liliumjsn/Edifier_R1280T_IR_Hack/Photos/IMG_20220609_170533.jpg

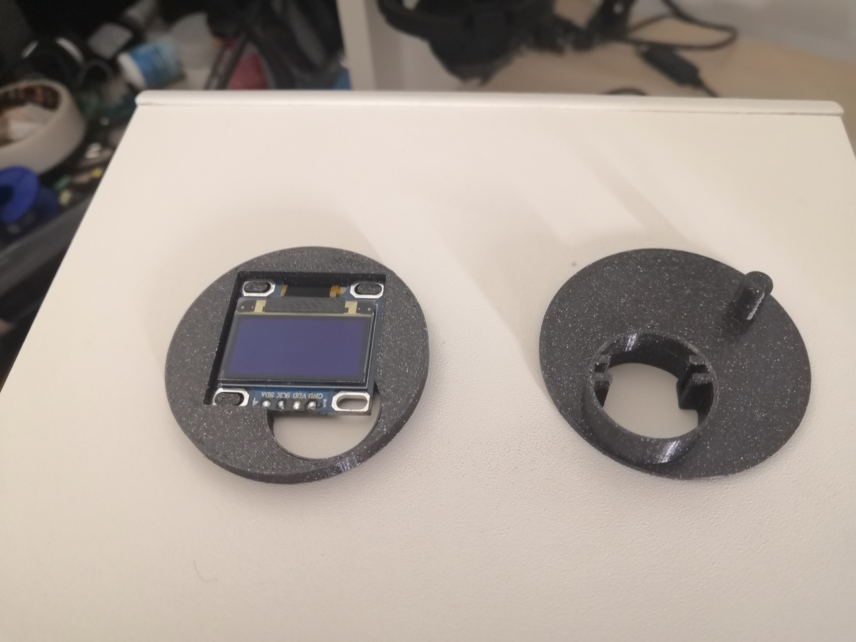
Photos/IMG_20220609_170533.jpg
