liliumjsn/Edifier_R1280T_IR_Hack/Software/src/icons.h

#include <Arduino.h>

// 'wifi_off_icon', 15x15px
const unsigned char epd_bitmap_wifi_off_icon [] PROGMEM = {
  0x01, 0x00, 0xF3, 0x07, 0x0E, 0x18, 0x0E, 0x20, 0x19, 0x40, 0xF0, 0x07, 
  0x6C, 0x18, 0xC2, 0x20, 0x80, 0x01, 0xE0, 0x03, 0x18, 0x0E, 0x00, 0x0C, 
  0xC0, 0x19, 0xC0, 0x31, 0xC0, 0x61, };
// 'wifi_on_icon', 15x15px
const unsigned char epd_bitmap_wifi_on_icon [] PROGMEM = {
  0x00, 0x00, 0xF0, 0x07, 0x0C, 0x18, 0x02, 0x20, 0x01, 0x40, 0xF0, 0x07, 
  0x0C, 0x18, 0x02, 0x20, 0x00, 0x00, 0xE0, 0x03, 0x18, 0x0C, 0x00, 0x00, 
  0xC0, 0x01, 0xC0, 0x01, 0xC0, 0x01, };

// 'mqtt_ok_icon', 15x15px
const unsigned char epd_bitmap_mqtt_ok_icon [] PROGMEM = {
  0x00, 0x00, 0x00, 0x00, 0x00, 0x00, 0x0C, 0x30, 0x1C, 0x38, 0x3C, 0x3C, 
  0x6C, 0x36, 0xCC, 0x33, 0x8C, 0x31, 0x0C, 0x30, 0x0C, 0x30, 0x0C, 0x30, 
  0x0C, 0x30, 0x00, 0x00, 0x00, 0x00, };

// 'mqtt_failed_icon', 15x15px
const unsigned char epd_bitmap_mqtt_failed_icon [] PROGMEM = {
  0x00, 0x00, 0x00, 0x00, 0xF8, 0x1F, 0xF8, 0x1F, 0x18, 0x00, 0x18, 0x00, 
  0x18, 0x00, 0xF8, 0x07, 0xF8, 0x07, 0x18, 0x00, 0x18, 0x00, 0x18, 0x00, 
  0x18, 0x00, 0x18, 0x00, 0x00, 0x00, };

// 'mute_icon', 50x50px
const uint8_t epd_bitmap_mute_icon [] PROGMEM = {
	0x00, 0x00, 0x00, 0x00, 0x00, 0x00, 0x00, 0x00, 0x00, 0x00, 0x00, 0x00, 
  0x00, 0x00, 0x00, 0x00, 0x00, 0x00, 0x00, 0x00, 0x00, 0x00, 0x00, 0x00, 
  0x00, 0x00, 0x00, 0x00, 0x00, 0x00, 0x00, 0x00, 0x00, 0x00, 0x00, 0x00, 
  0x00, 0x00, 0x18, 0x00, 0x00, 0x00, 0x00, 0x00, 0x00, 0x1C, 0x00, 0x00, 
  0x00, 0x00, 0x00, 0x00, 0x1E, 0x00, 0x00, 0x00, 0x00, 0x00, 0x00, 0x1F, 
  0x00, 0x00, 0x00, 0x00, 0x00, 0x80, 0x1F, 0x00, 0x00, 0x00, 0x00, 0x00, 
  0xC0, 0x1F, 0x00, 0x00, 0x00, 0x00, 0x00, 0xE0, 0x1F, 0x00, 0x00, 0x00, 
  0x00, 0x00, 0xF0, 0x1F, 0x00, 0x00, 0x00, 0x00, 0x00, 0xF8, 0x1F, 0x00, 
  0x00, 0x00, 0x00, 0x00, 0xFC, 0x1F, 0x00, 0x00, 0x00, 0xFE, 0xFF, 0xFF, 
  0x1F, 0x00, 0x00, 0x00, 0xFE, 0xFF, 0xFF, 0x9F, 0x01, 0xC0, 0x00, 0xFE, 
  0xFF, 0xFF, 0x1F, 0x03, 0x60, 0x00, 0xFE, 0xFF, 0xFF, 0x1F, 0x06, 0x30, 
  0x00, 0xFE, 0xFF, 0xFF, 0x1F, 0x0C, 0x18, 0x00, 0xFE, 0xFF, 0xFF, 0x1F, 
  0x18, 0x0C, 0x00, 0xFE, 0xFF, 0xFF, 0x1F, 0x30, 0x06, 0x00, 0xFE, 0xFF, 
  0xFF, 0x1F, 0x60, 0x03, 0x00, 0xFE, 0xFF, 0xFF, 0x1F, 0xC0, 0x01, 0x00, 
  0xFE, 0xFF, 0xFF, 0x1F, 0xC0, 0x01, 0x00, 0xFE, 0xFF, 0xFF, 0x1F, 0x60, 
  0x03, 0x00, 0xFE, 0xFF, 0xFF, 0x1F, 0x30, 0x06, 0x00, 0xFE, 0xFF, 0xFF, 
  0x1F, 0x18, 0x0C, 0x00, 0xFE, 0xFF, 0xFF, 0x1F, 0x0C, 0x18, 0x00, 0xFE, 
  0xFF, 0xFF, 0x1F, 0x06, 0x30, 0x00, 0xFE, 0xFF, 0xFF, 0x1F, 0x03, 0x60, 
  0x00, 0xFE, 0xFF, 0xFF, 0x9F, 0x01, 0xC0, 0x00, 0xFE, 0xFF, 0xFF, 0x1F, 
  0x00, 0x00, 0x00, 0xFE, 0xFF, 0xFF, 0x1F, 0x00, 0x00, 0x00, 0x00, 0x00, 
  0xFC, 0x1F, 0x00, 0x00, 0x00, 0x00, 0x00, 0xF8, 0x1F, 0x00, 0x00, 0x00, 
  0x00, 0x00, 0xF0, 0x1F, 0x00, 0x00, 0x00, 0x00, 0x00, 0xE0, 0x1F, 0x00, 
  0x00, 0x00, 0x00, 0x00, 0xC0, 0x1F, 0x00, 0x00, 0x00, 0x00, 0x00, 0x80, 
  0x1F, 0x00, 0x00, 0x00, 0x00, 0x00, 0x00, 0x1F, 0x00, 0x00, 0x00, 0x00, 
  0x00, 0x00, 0x1E, 0x00, 0x00, 0x00, 0x00, 0x00, 0x00, 0x1C, 0x00, 0x00, 
  0x00, 0x00, 0x00, 0x00, 0x18, 0x00, 0x00, 0x00, 0x00, 0x00, 0x00, 0x00, 
  0x00, 0x00, 0x00, 0x00, 0x00, 0x00, 0x00, 0x00, 0x00, 0x00, 0x00, 0x00, 
  0x00, 0x00, 0x00, 0x00, 0x00, 0x00, 0x00, 0x00, 0x00, 0x00, 0x00, 0x00, 
  0x00, 0x00, 0x00, 0x00, 0x00, 0x00, 0x00, 0x00, 0x00, 0x00, 0x00, 0x00, 
  0x00, 0x00, };
